teddycool/Sensordevice/20200407_090734.jpg

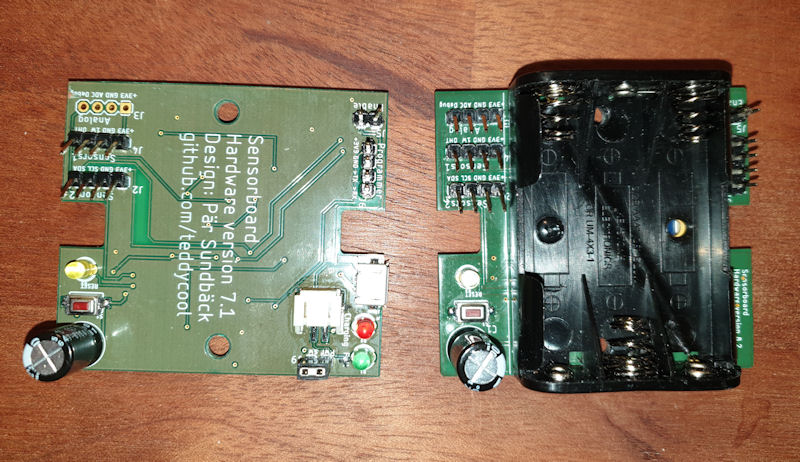
20200407_090734.jpg
