teddycool/Sensordevice/HW/ESP8266-HW8/20191026_080203.jpg

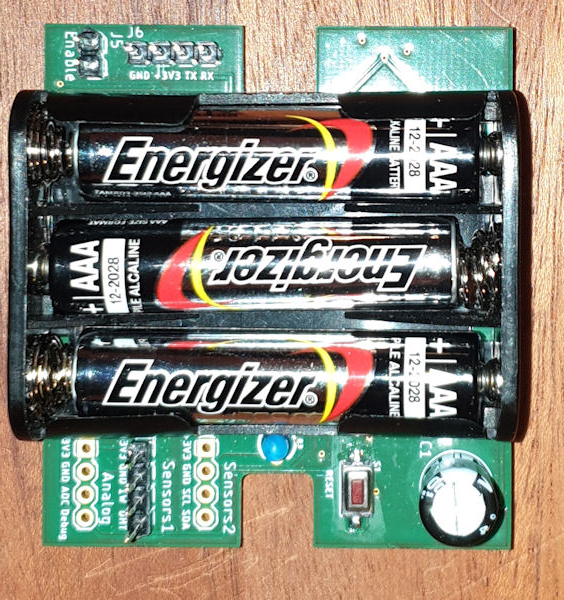
HW/ESP8266-HW8/20191026_080203.jpg
