teddycool/Sensordevice/HW/ESP8266-HW8/20191026_191500.jpg

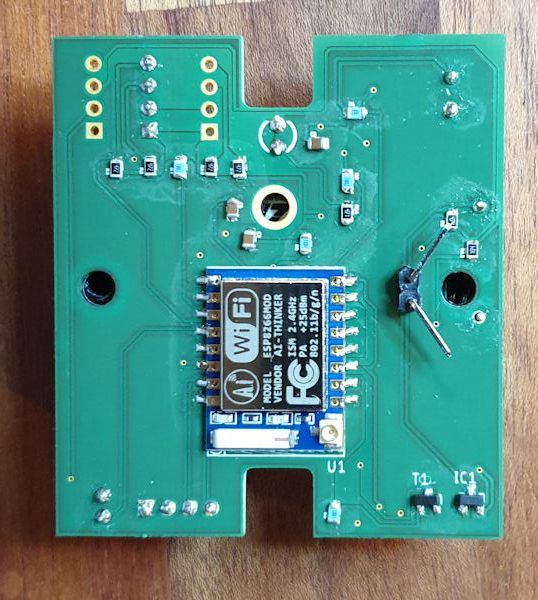
HW/ESP8266-HW8/20191026_191500.jpg
